Szbuli/alarm-controller/firmware/f103_alarm_modul/Core/Src/config/home_config.c

/*
 * home_config.c
 *
 *  Created on: 2017.05.23.
 *      Author: Szbuli
 */

#include "home_config.h"
#include "can_support.h"
#include "eeprom.h"
#include "can-ids.h"
#include "gpio.h"

HomeConfig homeConfig;

void blinkRapid() {
	HAL_GPIO_WritePin(BUSY_LED_GPIO_Port, BUSY_LED_Pin, GPIO_PIN_RESET);
	osDelay(50);
	HAL_GPIO_WritePin(BUSY_LED_GPIO_Port, BUSY_LED_Pin, GPIO_PIN_SET);
	osDelay(50);
	HAL_GPIO_WritePin(BUSY_LED_GPIO_Port, BUSY_LED_Pin, GPIO_PIN_RESET);
	osDelay(50);
	HAL_GPIO_WritePin(BUSY_LED_GPIO_Port, BUSY_LED_Pin, GPIO_PIN_SET);
	osDelay(50);
	HAL_GPIO_WritePin(BUSY_LED_GPIO_Port, BUSY_LED_Pin, GPIO_PIN_RESET);
}

void checkAndDoFactoryResetIfNeeded() {
	GPIO_PinState factoryResetState = HAL_GPIO_ReadPin(FACTORY_RESET_GPIO_Port, FACTORY_RESET_Pin);
	if (factoryResetState == GPIO_PIN_SET) {
		return;
	}

	osDelay(5000);
	factoryResetState = HAL_GPIO_ReadPin(FACTORY_RESET_GPIO_Port, FACTORY_RESET_Pin);
	if (factoryResetState == GPIO_PIN_SET) {
		HAL_GPIO_WritePin(BUSY_LED_GPIO_Port, BUSY_LED_Pin, GPIO_PIN_RESET);
		return;
	}
	blinkRapid();
	HAL_GPIO_WritePin(BUSY_LED_GPIO_Port, BUSY_LED_Pin, GPIO_PIN_SET);
	factoryReset();
	blinkRapid();
	HAL_NVIC_SystemReset();
}

void configureTamper(uint8_t state) {
	writeByteEEPROM(ADDRESS_TAMPER, state);

	osDelay(100);
	HAL_NVIC_SystemReset();
}

void configureHeartbeat(uint8_t state) {
	writeByteEEPROM(ADDRESS_HEARTBEAT, state);

	osDelay(100);
	HAL_NVIC_SystemReset();
}

void configureSensor(uint16_t typeId, uint8_t state) {
	if (typeId == ALARM_CONTROLLER_CONFIGURE_SENSOR_1) {
		writeByteEEPROM(ADDRESS_ALARM_1, state);
	} else if (typeId == ALARM_CONTROLLER_CONFIGURE_SENSOR_2) {
		writeByteEEPROM(ADDRESS_ALARM_2, state);
	} else if (typeId == ALARM_CONTROLLER_CONFIGURE_SENSOR_3) {
		writeByteEEPROM(ADDRESS_ALARM_3, state);
	} else if (typeId == ALARM_CONTROLLER_CONFIGURE_SENSOR_4) {
		writeByteEEPROM(ADDRESS_ALARM_4, state);
	} else if (typeId == ALARM_CONTROLLER_CONFIGURE_SENSOR_5) {
		writeByteEEPROM(ADDRESS_ALARM_5, state);
	} else if (typeId == ALARM_CONTROLLER_CONFIGURE_SENSOR_6) {
		writeByteEEPROM(ADDRESS_ALARM_6, state);
	} else if (typeId == ALARM_CONTROLLER_CONFIGURE_SENSOR_7) {
		writeByteEEPROM(ADDRESS_ALARM_7, state);
	} else if (typeId == ALARM_CONTROLLER_CONFIGURE_SENSOR_8) {
		writeByteEEPROM(ADDRESS_ALARM_8, state);
	} else if (typeId == ALARM_CONTROLLER_CONFIGURE_SENSOR_9) {
		writeByteEEPROM(ADDRESS_ALARM_9, state);
	} else if (typeId == ALARM_CONTROLLER_CONFIGURE_SENSOR_10) {
		writeByteEEPROM(ADDRESS_ALARM_10, state);
	} else if (typeId == ALARM_CONTROLLER_CONFIGURE_SENSOR_11) {
		writeByteEEPROM(ADDRESS_ALARM_11, state);
	} else if (typeId == ALARM_CONTROLLER_CONFIGURE_SENSOR_12) {
		writeByteEEPROM(ADDRESS_ALARM_12, state);
	} else if (typeId == ALARM_CONTROLLER_CONFIGURE_SENSOR_13) {
		writeByteEEPROM(ADDRESS_ALARM_13, state);
	} else if (typeId == ALARM_CONTROLLER_CONFIGURE_SENSOR_14) {
		writeByteEEPROM(ADDRESS_ALARM_14, state);
	} else if (typeId == ALARM_CONTROLLER_CONFIGURE_SENSOR_15) {
		writeByteEEPROM(ADDRESS_ALARM_15, state);
	}

	osDelay(100);
	HAL_NVIC_SystemReset();
}

void configureCounterCurrentValue(uint16_t typeId, uint64_t counterValue) {
	if (typeId == ALARM_CONTROLLER_COUNTER_SET_1) {
		write8ByteEEPROM(ADDRESS_COUNTER_1, counterValue);
	} else if (typeId == ALARM_CONTROLLER_COUNTER_SET_2) {
		write8ByteEEPROM(ADDRESS_COUNTER_2, counterValue);
	} else if (typeId == ALARM_CONTROLLER_COUNTER_SET_3) {
		write8ByteEEPROM(ADDRESS_COUNTER_3, counterValue);
	} else if (typeId == ALARM_CONTROLLER_COUNTER_SET_4) {
		write8ByteEEPROM(ADDRESS_COUNTER_4, counterValue);
	} else if (typeId == ALARM_CONTROLLER_COUNTER_SET_5) {
		write8ByteEEPROM(ADDRESS_COUNTER_5, counterValue);
	} else if (typeId == ALARM_CONTROLLER_COUNTER_SET_6) {
		write8ByteEEPROM(ADDRESS_COUNTER_6, counterValue);
	} else if (typeId == ALARM_CONTROLLER_COUNTER_SET_7) {
		write8ByteEEPROM(ADDRESS_COUNTER_7, counterValue);
	} else if (typeId == ALARM_CONTROLLER_COUNTER_SET_8) {
		write8ByteEEPROM(ADDRESS_COUNTER_8, counterValue);
	} else if (typeId == ALARM_CONTROLLER_COUNTER_SET_9) {
		write8ByteEEPROM(ADDRESS_COUNTER_9, counterValue);
	} else if (typeId == ALARM_CONTROLLER_COUNTER_SET_10) {
		write8ByteEEPROM(ADDRESS_COUNTER_10, counterValue);
	} else if (typeId == ALARM_CONTROLLER_COUNTER_SET_11) {
		write8ByteEEPROM(ADDRESS_COUNTER_11, counterValue);
	} else if (typeId == ALARM_CONTROLLER_COUNTER_SET_12) {
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
	homeConfig.alarm_11 = readByteEEPROM(ADDRESS_ALARM_11);
	homeConfig.alarm_12 = readByteEEPROM(ADDRESS_ALARM_12);
	homeConfig.alarm_13 = readByteEEPROM(ADDRESS_ALARM_13);
	homeConfig.alarm_14 = readByteEEPROM(ADDRESS_ALARM_14);
	homeConfig.alarm_15 = readByteEEPROM(ADDRESS_ALARM_15);
}

void factoryReset() {
	writeByteEEPROM(ADDRESS_DEVICE_ID_PART_0, 0xFF);
	writeByteEEPROM(ADDRESS_DEVICE_ID_PART_1, 0xFF);
	writeByteEEPROM(ADDRESS_TAMPER, 0);
	writeByteEEPROM(ADDRESS_HEARTBEAT, 1);
	writeByteEEPROM(ADDRESS_ALARM_1, 0);
	writeByteEEPROM(ADDRESS_ALARM_2, 0);
	writeByteEEPROM(ADDRESS_ALARM_3, 0);
	writeByteEEPROM(ADDRESS_ALARM_4, 0);
	writeByteEEPROM(ADDRESS_ALARM_5, 0);
	writeByteEEPROM(ADDRESS_ALARM_6, 0);
	writeByteEEPROM(ADDRESS_ALARM_7, 0);
	writeByteEEPROM(ADDRESS_ALARM_8, 0);
	writeByteEEPROM(ADDRESS_ALARM_9, 0);
	writeByteEEPROM(ADDRESS_ALARM_10, 0);
	writeByteEEPROM(ADDRESS_ALARM_11, 0);
	writeByteEEPROM(ADDRESS_ALARM_12, 0);
	writeByteEEPROM(ADDRESS_ALARM_13, 0);
	writeByteEEPROM(ADDRESS_ALARM_14, 0);
	writeByteEEPROM(ADDRESS_ALARM_15, 0);
}
